francfly12/PZEM004-smartmeter/20240416_231157.jpg

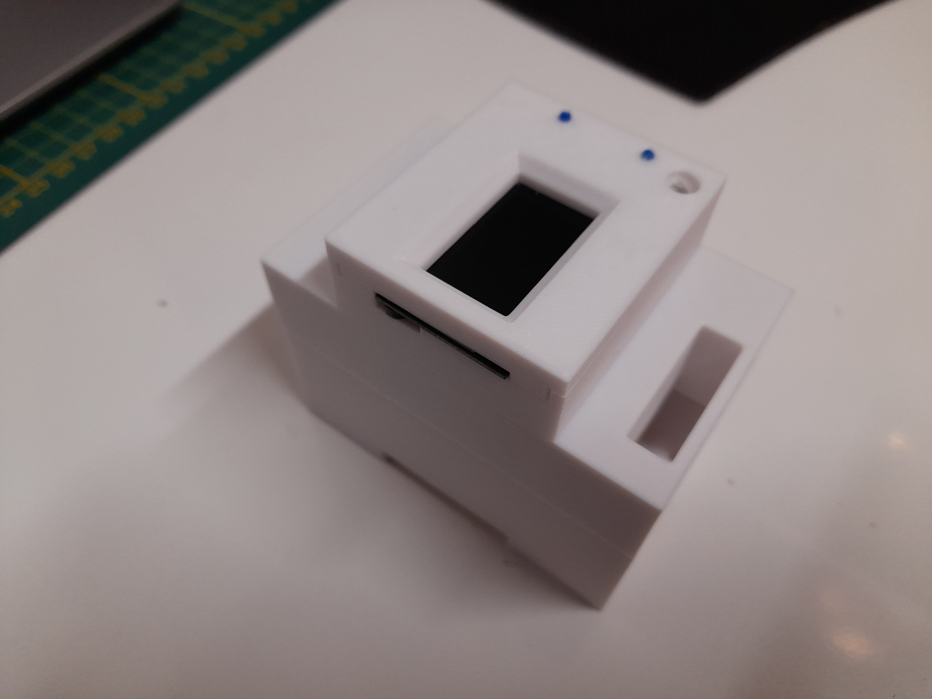
20240416_231157.jpg
