francfly12/PZEM004-smartmeter/20240418_105911.jpg

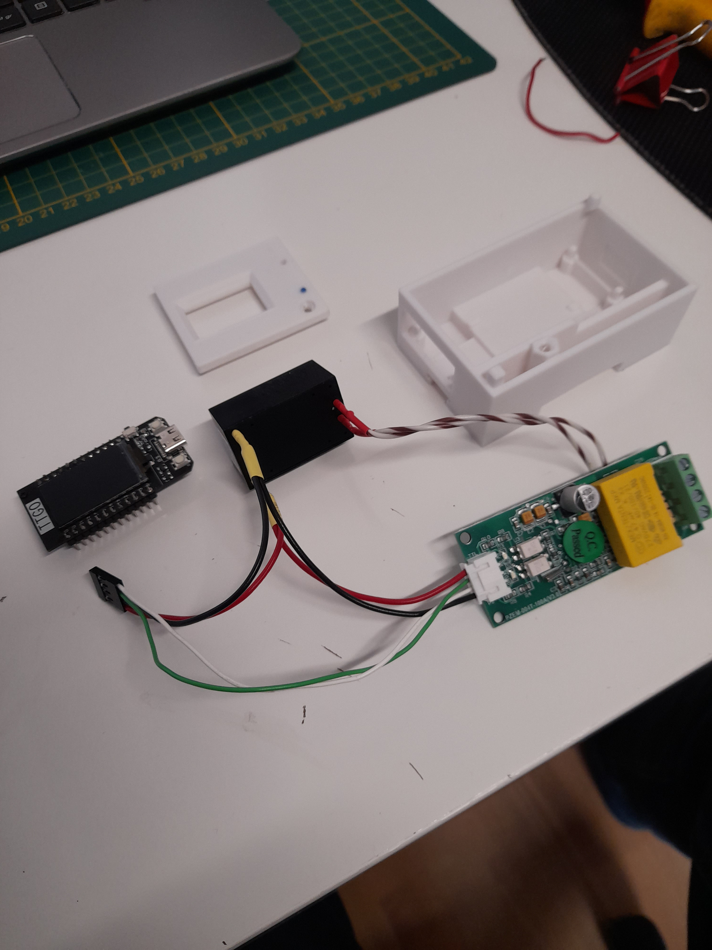
20240418_105911.jpg
