francfly12/PZEM004-smartmeter/20240418_110554.jpg

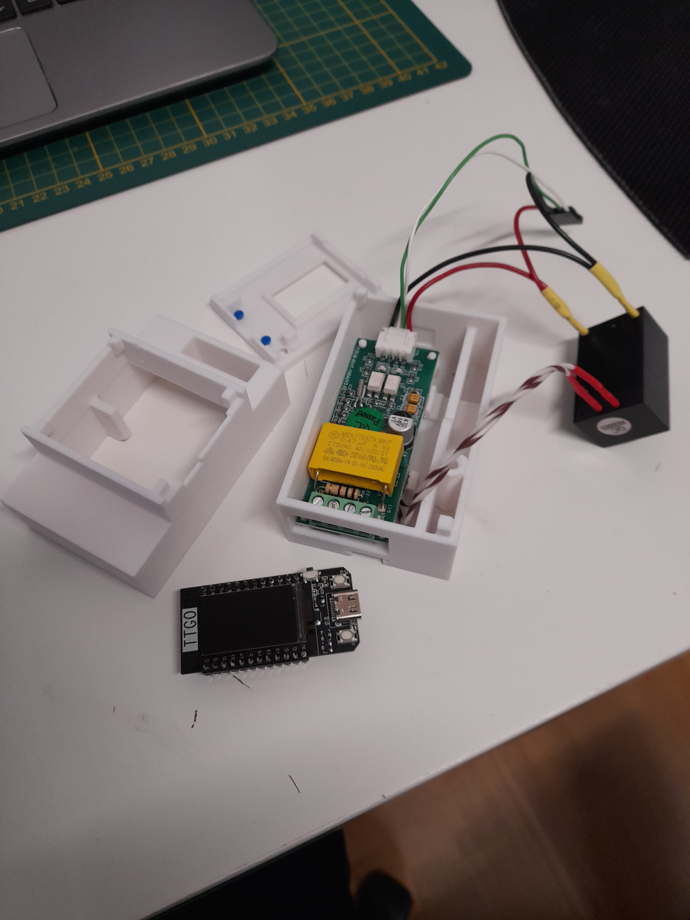
20240418_110554.jpg
