francfly12/PZEM004-smartmeter/20240421_192325.jpg

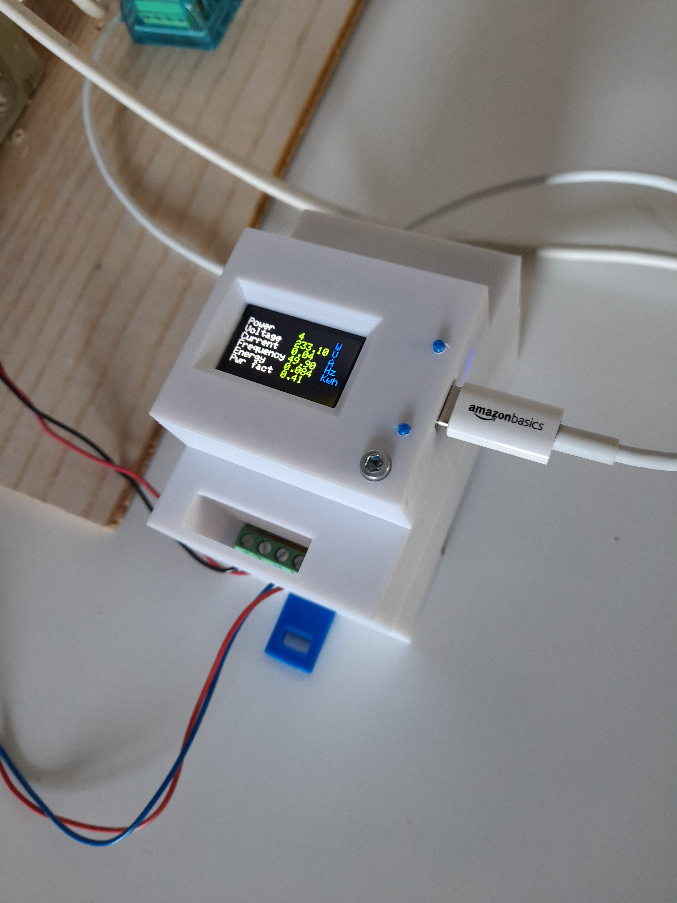
20240421_192325.jpg
