francfly12/PZEM004-smartmeter/20240506_161026.jpg

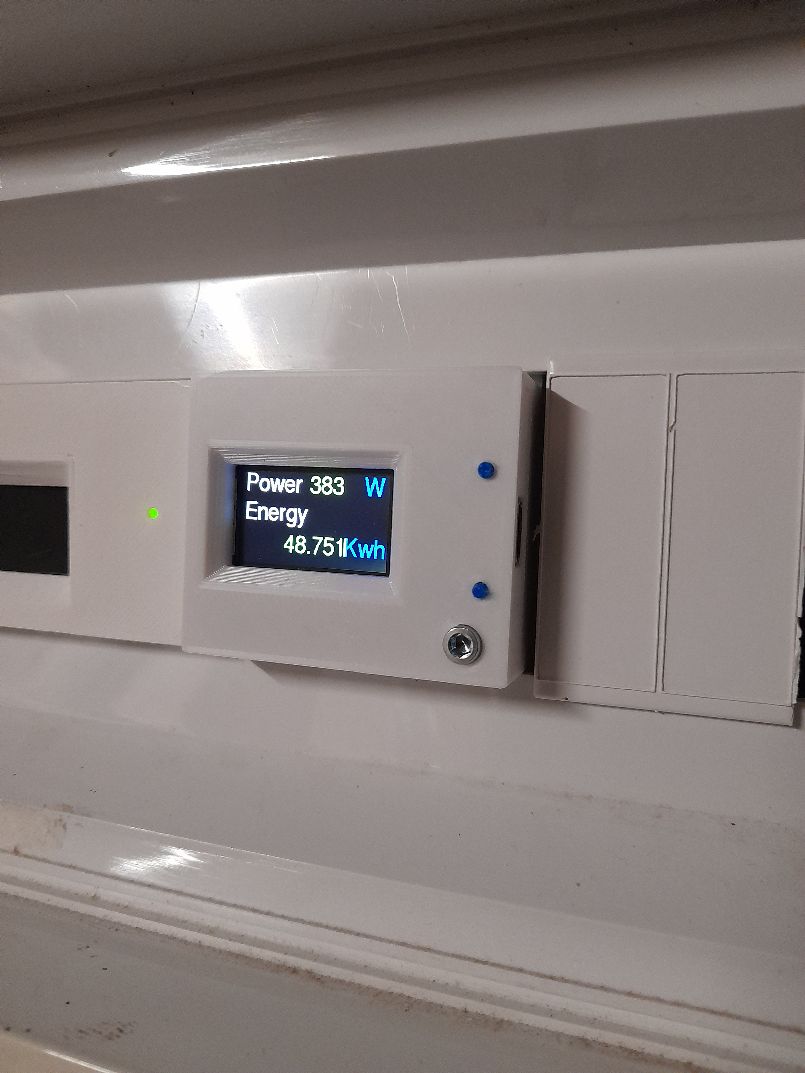
20240506_161026.jpg
