francfly12/PZEM004-smartmeter/20240506_161120.jpg

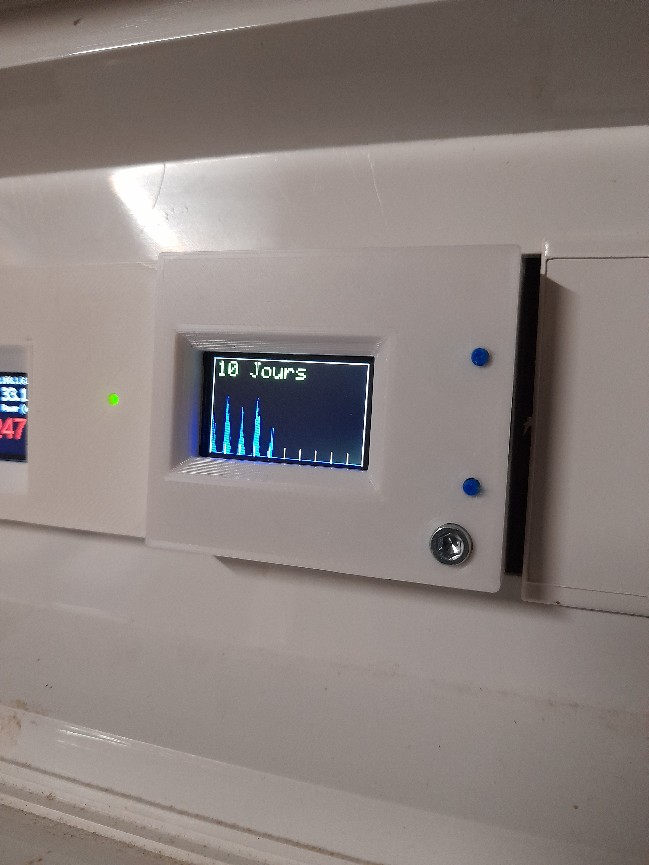
20240506_161120.jpg
